TripleTrable/OpenMTB/schematics/backplane/backplane/backplane.kicad_sch

## KiCad design schematics/backplane/backplane/backplane.kicad_sch (2025-02-17, an earlier design)

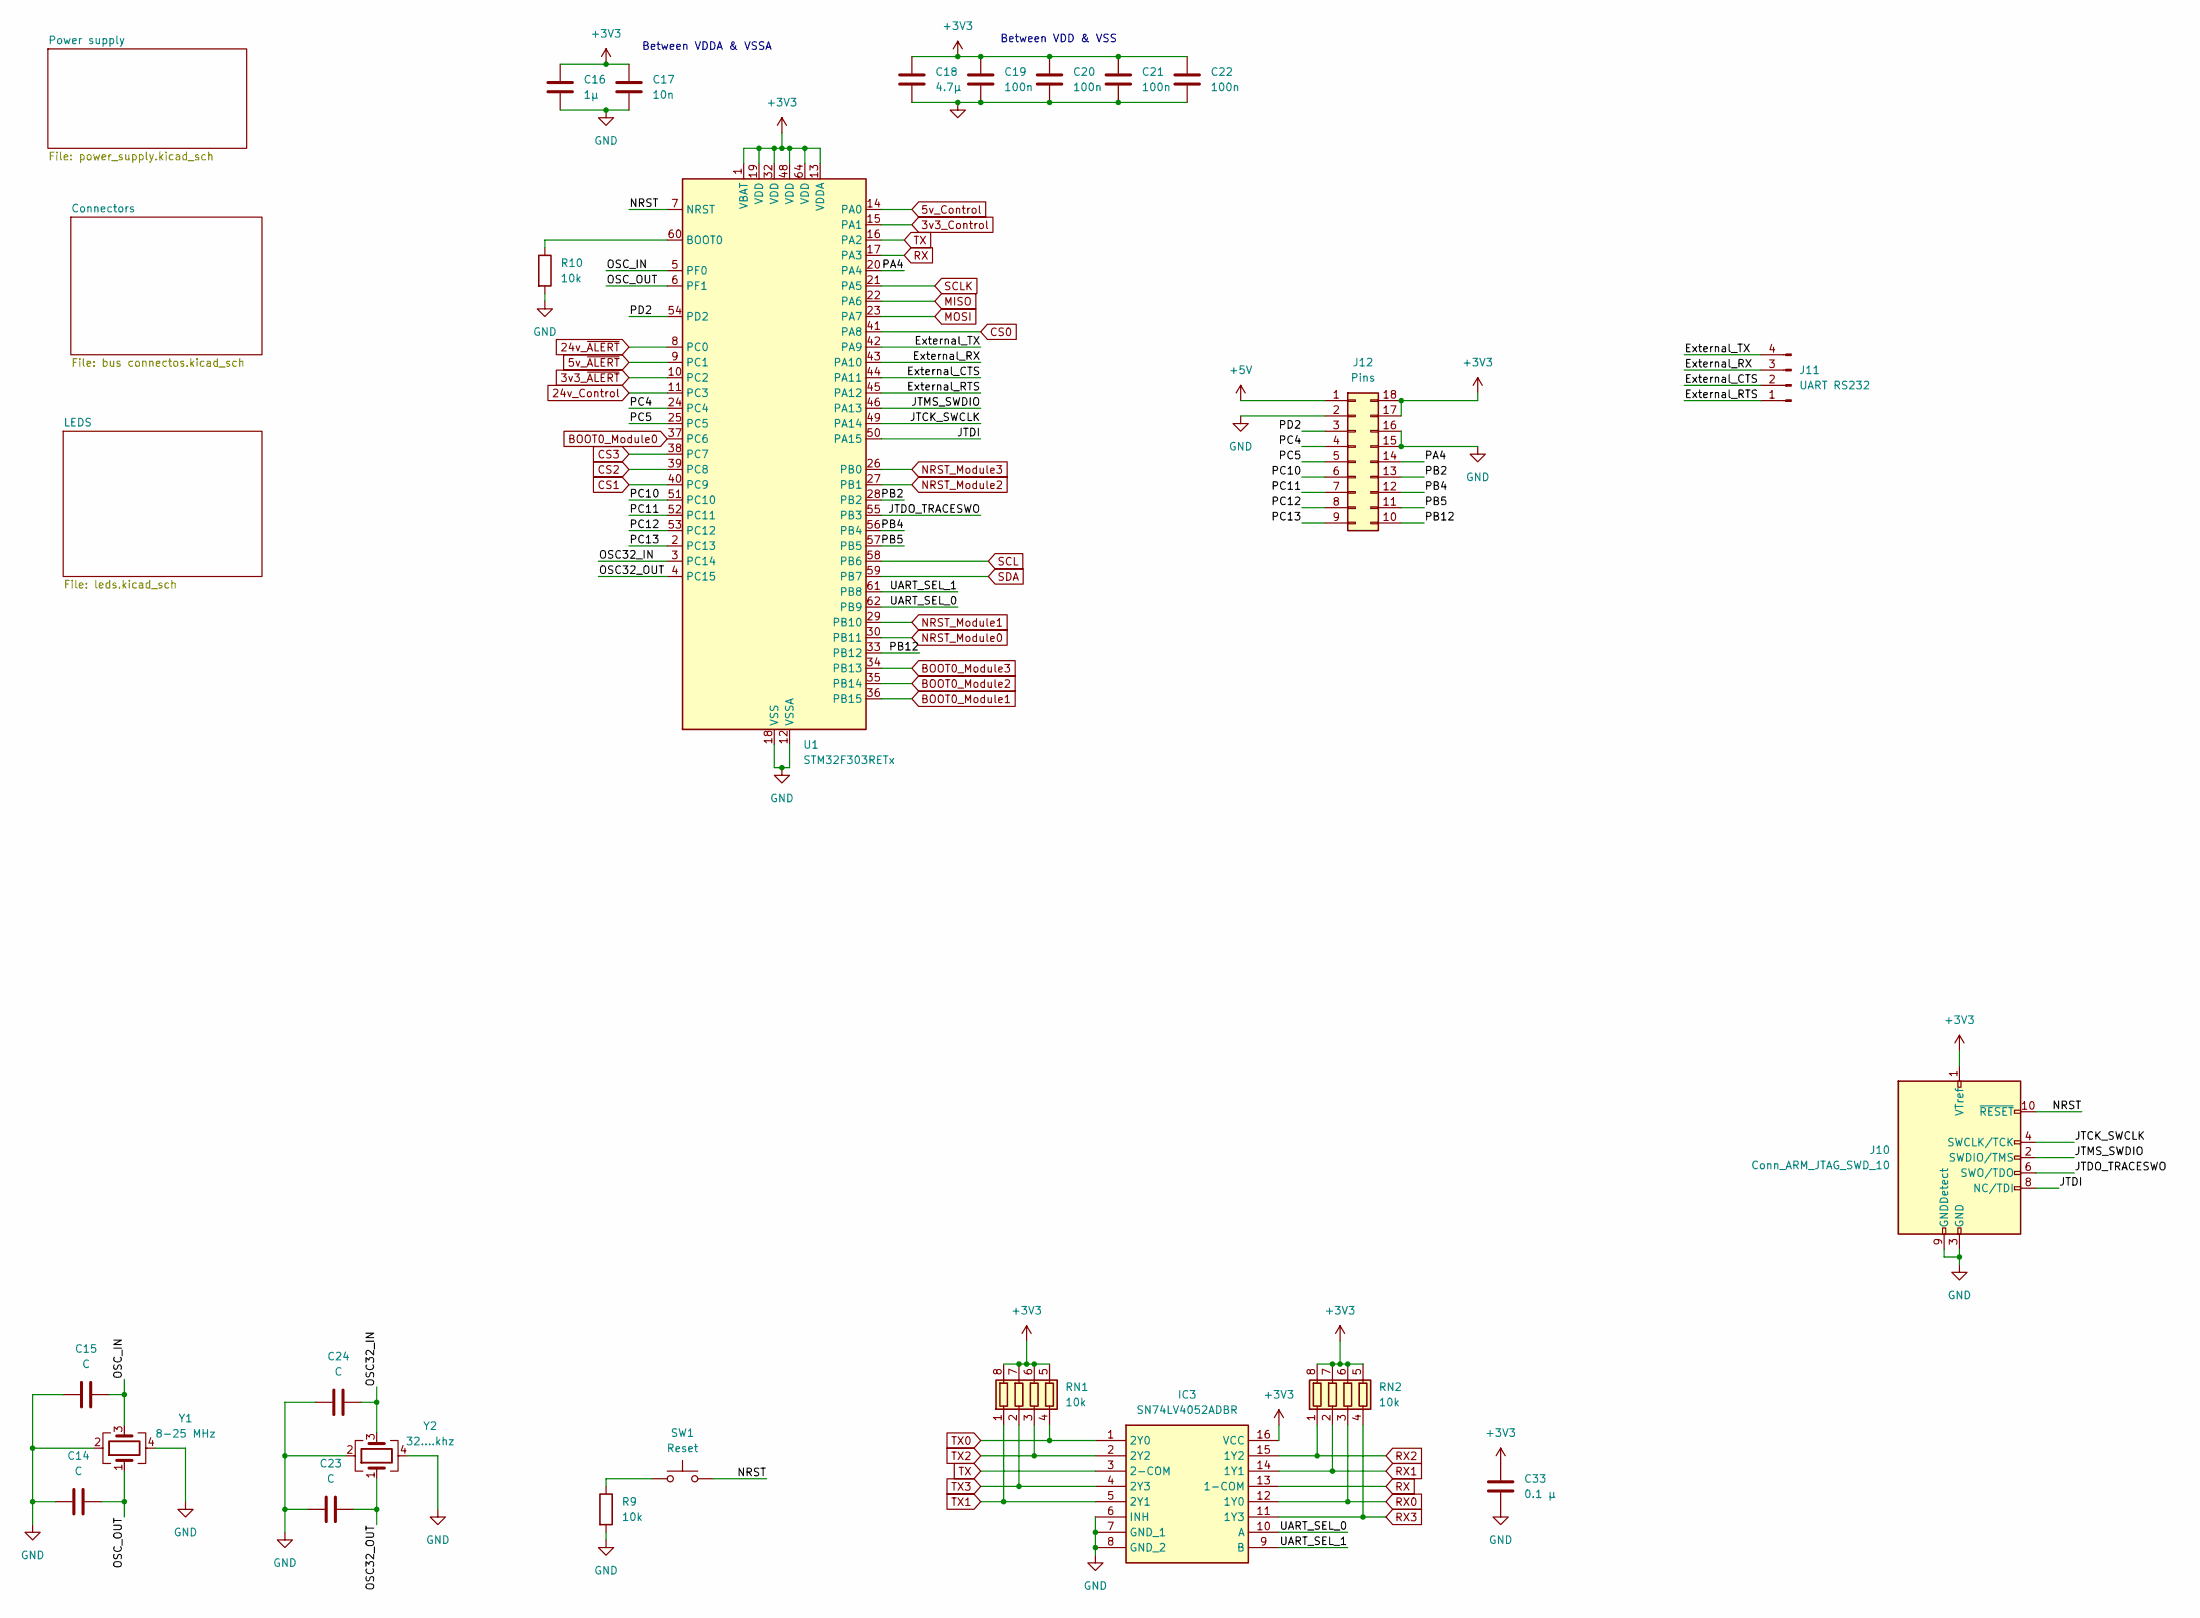
[picture p2: schematic backplane.kicad_sch]

Parts:
C14, C15, C23, C24: C; C_0603_1608Metric
C16: 1µ; C_0603_1608Metric
C17: 10n; C_0603_1608Metric
C18: 4.7µ; C_0603_1608Metric
C19, C20, C21, C22: 100n; C_0603_1608Metric
C33: 0.1 μ; C_0603_1608Metric
IC3: SN74LV4052ADBR; SOP65P780X200-16N; Mouser Part Number 595-SN74LV4052ADBR
J10: Conn_ARM_JTAG_SWD_10; PinHeader_2x05_P1.27mm_Vertical_SMD
J11: UART RS232; PinHeader_1x04_P2.54mm_Vertical_SMD_Pin1Left
J12: Pins; PinHeader_2x09_P2.54mm_Vertical
R9, R10: 10k; R_0603_1608Metric
RN1, RN2: 10k; R_Array_Convex_4x0603
SW1: Reset; SW_SPST_Omron_B3FS-100xP
U1: STM32F303RETx; LQFP-64_10x10mm_P0.5mm
Y1: 8-25 MHz
Y2: 32....khz

Connections:
3v3_Control: U1.15 (PA1)
3v3_~ALERT: U1.10 (PC2)
5v_Control: U1.14 (PA0)
5v_~ALERT: U1.9 (PC1)
24v_Control: U1.11 (PC3)
24v_~ALERT: U1.8 (PC0)
+3V3: C16.1, C17.1, C18.1, C19.1, C20.1, C21.1, C22.1, C33.1, IC3.16 (VCC), J10.1 (VTref), J12.17, J12.18, RN1.5 (R4.2), RN1.6 (R3.2), RN1.7 (R2.2), RN1.8 (R1.2), RN2.5 (R4.2), RN2.6 (R3.2), RN2.7 (R2.2), RN2.8 (R1.2), U1.1 (VBAT), U1.13 (VDDA), U1.19 (VDD), U1.32 (VDD), U1.48 (VDD), U1.64 (VDD)
+5V: J12.1
BOOT0_Module0: U1.37 (PC6)
BOOT0_Module1: U1.36 (PB15)
BOOT0_Module2: U1.35 (PB14)
BOOT0_Module3: U1.34 (PB13)
CS0: U1.41 (PA8)
CS1: U1.40 (PC9)
CS2: U1.39 (PC8)
CS3: U1.38 (PC7)
External_CTS: J11.2, U1.44 (PA11)
External_RTS: J11.1, U1.45 (PA12)
External_RX: J11.3, U1.43 (PA10)
External_TX: J11.4, U1.42 (PA9)
GND: C14.1, C15.1, C16.2, C17.2, C18.2, C19.2, C20.2, C21.2, C22.2, C23.1, C24.1, C33.2, IC3.6 (INH), IC3.7 (GND_1), IC3.8 (GND_2), J10.3 (GND), J10.5 (GND), J10.9 (GNDDetect), J12.2, J12.15, J12.16, R9.2, R10.2, U1.12 (VSSA), U1.18 (VSS), U1.31 (VSS), U1.47 (VSS), U1.63 (VSS), Y1.2, Y1.4, Y2.2, Y2.4
JTCK_SWCLK: J10.4 (SWCLK/TCK), U1.49 (PA14)
JTDI: J10.8 (NC/TDI), U1.50 (PA15)
JTDO_TRACESWO: J10.6 (SWO/TDO), U1.55 (PB3)
JTMS_SWDIO: J10.2 (SWDIO/TMS), U1.46 (PA13)
MISO: U1.22 (PA6)
MOSI: U1.23 (PA7)
NRST: J10.10 (~RESET), SW1.2, U1.7 (NRST)
NRST_Module0: U1.30 (PB11)
NRST_Module1: U1.29 (PB10)
NRST_Module2: U1.27 (PB1)
NRST_Module3: U1.26 (PB0)
unnamed: R9.1, SW1.1
unnamed: R10.1, U1.60 (BOOT0)
OSC32_IN: C24.2, U1.3 (PC14), Y2.3
OSC32_OUT: C23.2, U1.4 (PC15), Y2.1
OSC_IN: C15.2, U1.5 (PF0), Y1.3
OSC_OUT: C14.2, U1.6 (PF1), Y1.1
PA4: J12.14, U1.20 (PA4)
PB2: J12.13, U1.28 (PB2)
PB4: J12.12, U1.56 (PB4)
PB5: J12.11, U1.57 (PB5)
PB12: J12.10, U1.33 (PB12)
PC4: J12.4, U1.24 (PC4)
PC5: J12.5, U1.25 (PC5)
PC10: J12.6, U1.51 (PC10)
PC11: J12.7, U1.52 (PC11)
PC12: J12.8, U1.53 (PC12)
PC13: J12.9, U1.2 (PC13)
PD2: J12.3, U1.54 (PD2)
RX: IC3.13 (1-COM), U1.17 (PA3)
RX0: IC3.12 (1Y0), RN2.3 (R3.1)
RX1: IC3.14 (1Y1), RN2.2 (R2.1)
RX2: IC3.15 (1Y2), RN2.1 (R1.1)
RX3: IC3.11 (1Y3), RN2.4 (R4.1)
SCL: U1.58 (PB6)
SCLK: U1.21 (PA5)
SDA: U1.59 (PB7)
TX: IC3.3 (2-COM), U1.16 (PA2)
TX0: IC3.1 (2Y0), RN1.4 (R4.1)
TX1: IC3.5 (2Y1), RN1.1 (R1.1)
TX2: IC3.2 (2Y2), RN1.3 (R3.1)
TX3: IC3.4 (2Y3), RN1.2 (R2.1)
UART_SEL_0: IC3.10 (A), U1.62 (PB9)
UART_SEL_1: IC3.9 (B), U1.61 (PB8)

Notes on the sheet:
Between VDD & VSS
Between VDDA & VSSA
