TripleTrable/OpenMTB/schematics/backplane/backplane/leds.kicad_sch

## KiCad design schematics/backplane/backplane/leds.kicad_sch (2025-02-17, an earlier design)

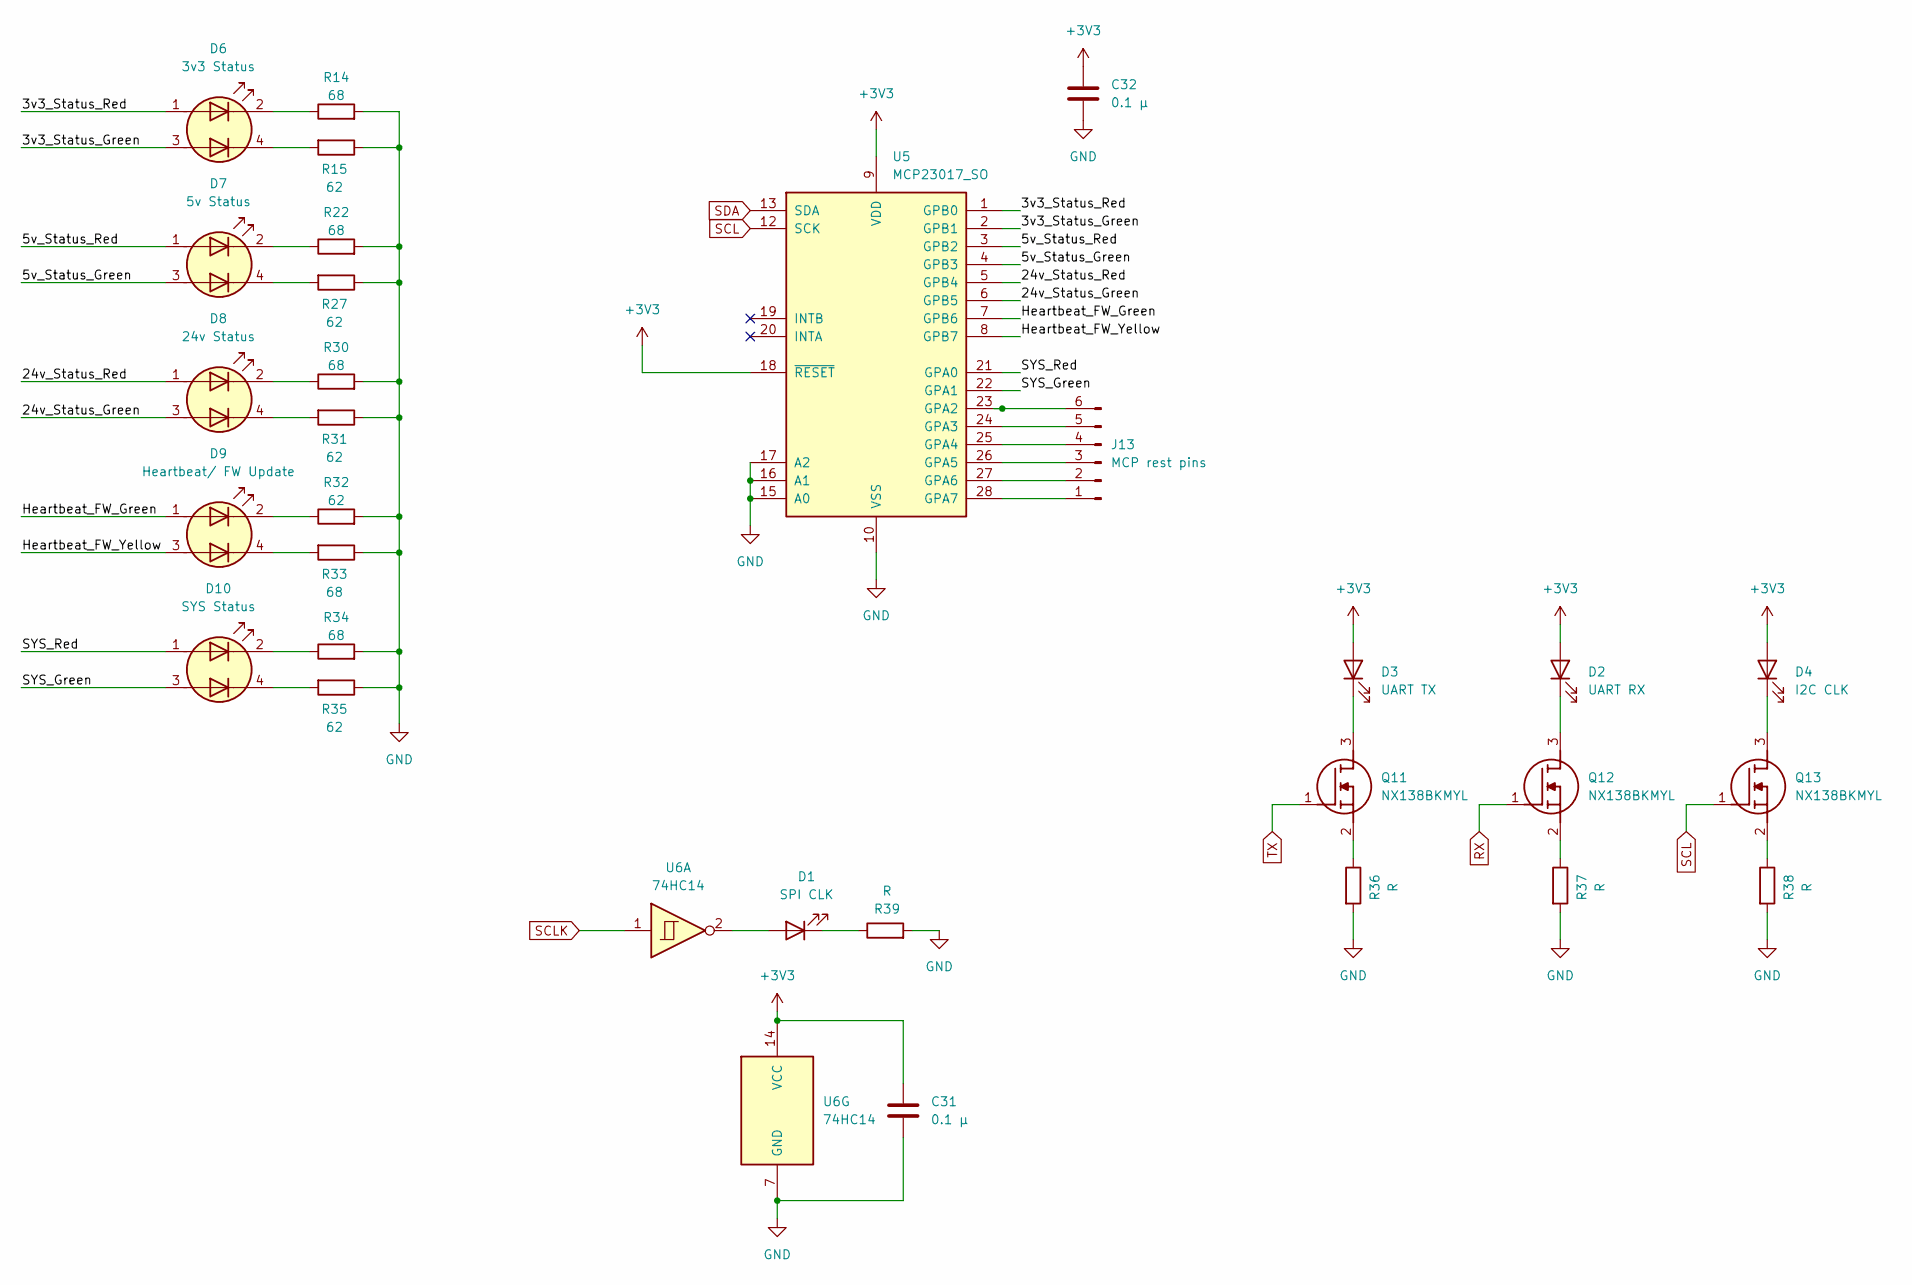
[picture p4: schematic leds.kicad_sch]

Parts:
C31, C32: 0.1 μ; C_0603_1608Metric
D1: SPI CLK; LED_0805_2012Metric
D2: UART RX; LED_0805_2012Metric
D3: UART TX; LED_0805_2012Metric
D4: I2C CLK; LED_0805_2012Metric
D6: 3v3 Status; APBA2006SURKCGKC
D7: 5v Status; APBA2006SURKCGKC
D8: 24v Status; APBA2006SURKCGKC
D9: Heartbeat/ FW Update; APBA2006SURKCGKC
D10: SYS Status; APBA2006SURKCGKC
J13: MCP rest pins; PinHeader_1x06_P2.54mm_Vertical_SMD_Pin1Left
Q11, Q12, Q13: NX138BKMYL; Mouser Part Number 771-NX138BKMYL
R14, R22, R30, R33, R34: 68; R_0603_1608Metric
R15, R27, R31, R32, R35: 62; R_0603_1608Metric
R36, R37, R38, R39: R; R_0603_1608Metric
U5: MCP23017_SO; SOIC-28W_7.5x17.9mm_P1.27mm
U6: 74HC14; TSSOP-14_4.4x5mm_P0.65mm

Connections:
3v3_Status_Green: D6.3 (A2), U5.2 (GPB1)
3v3_Status_Red: D6.1 (A1), U5.1 (GPB0)
5v_Status_Green: D7.3 (A2), U5.4 (GPB3)
5v_Status_Red: D7.1 (A1), U5.3 (GPB2)
24v_Status_Green: D8.3 (A2), U5.6 (GPB5)
24v_Status_Red: D8.1 (A1), U5.5 (GPB4)
+3V3: C31.1, C32.1, D2.2 (A), D3.2 (A), D4.2 (A), U5.9 (VDD), U5.18 (~RESET), U6.14 (VCC)
GND: C31.2, C32.2, R14.2, R15.1, R22.2, R27.1, R30.2, R31.1, R32.2, R33.1, R34.2, R35.1, R36.2, R37.2, R38.2, R39.2, U5.10 (VSS), U5.15 (A0), U5.16 (A1), U5.17 (A2), U6.7 (GND)
Heartbeat_FW_Green: D9.1 (A1), U5.7 (GPB6)
Heartbeat_FW_Yellow: D9.3 (A2), U5.8 (GPB7)
unnamed: D1.1 (K), R39.1
unnamed: D1.2 (A), U6.2
unnamed: D2.1 (K), Q12.3 (D)
unnamed: D3.1 (K), Q11.3 (D)
unnamed: D4.1 (K), Q13.3 (D)
unnamed: D6.2 (K1), R14.1
unnamed: D6.4 (K2), R15.2
unnamed: D7.2 (K1), R22.1
unnamed: D7.4 (K2), R27.2
unnamed: D8.2 (K1), R30.1
unnamed: D8.4 (K2), R31.2
unnamed: D9.2 (K1), R32.1
unnamed: D9.4 (K2), R33.2
unnamed: D10.2 (K1), R34.1
unnamed: D10.4 (K2), R35.2
unnamed: J13.1, U5.28 (GPA7)
unnamed: J13.2, U5.27 (GPA6)
unnamed: J13.3, U5.26 (GPA5)
unnamed: J13.4, U5.25 (GPA4)
unnamed: J13.5, U5.24 (GPA3)
unnamed: J13.6, U5.23 (GPA2)
unnamed: Q11.2 (S), R36.1
unnamed: Q12.2 (S), R37.1
unnamed: Q13.2 (S), R38.1
RX: Q12.1 (G)
SCL: Q13.1 (G), U5.12 (SCK)
SCLK: U6.1
SDA: U5.13 (SDA)
SYS_Green: D10.3 (A2), U5.22 (GPA1)
SYS_Red: D10.1 (A1), U5.21 (GPA0)
TX: Q11.1 (G)
